tilaktilak/Variometre/schematic/sd_reader.jpg

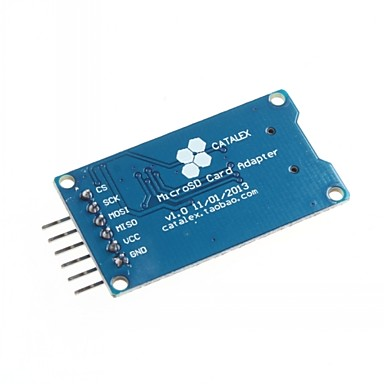
schematic/sd_reader.jpg
